ffxx283/VS1053_MP3/VS1053/Code/01_Debug/02_Evl/soundpressure.h

#ifndef SOUNDPRESSURE_H
#define SOUNDPRESSURE_H


u_int16 LinToDB(u_int16 n);
void DrawSoundPressureBars(register s_int16 *samplePair, register u_int16 *levelmem);
void DrawSoundPressureArea();

#endif 
