ffxx283/VS1053_MP3/VS1053/Code/01_Debug/02_Evl/spi.h

#ifndef SPI_H
#define SPI_H

auto u_int16 SpiSend(register __a0 u_int16 dataTopAligned, register __a1 bits);
auto u_int16 SpiTransfer(register __a0 u_int16 dataTopAligned, register __a1 bits);




#endif
