ffxx283/VS1053_MP3/VS1053/Code/01_Debug/02_Evl/vlsilogo.c

#include <vstypes.h>
#include "vlsilogo.h"
const u_int16 vlsilogo[] = {
	0xC618,0xBDF7,0xB5B7,0x6C36,0x3B15,0x3B15,0x7C76,0xBDF7,0xC618,0xC618,0xC618,0xC618,0xC618,0xC618,0xC618,0xC618,0xC618,0xC618,0xC618,0xC618,0xC618,
	0xBDF7,0xA577,0x32F5,0xE75E,0x2AD5,0x9D9A,0xE75E,0x9516,0x9CD3,0x4208,0xC618,0x4208,0x9CD3,0x3186,0xC618,0xC618,0x73AE,0x20E4,0x6B6D,0xC618,0x4A29,
	0xB5D7,0x3B15,0x2AD5,0xE75E,0x9D9A,0x2AD5,0xE75E,0x63D5,0x9CD3,0x20E4,0xC618,0x20E4,0x9CD3,0x20E4,0xC618,0xC618,0x20E4,0xC618,0x7BCF,0xC618,0x20E4,
	0x7C76,0x9D9A,0xE75E,0x2AD5,0x9D9A,0xE75E,0x2AD5,0x63F5,0xC618,0x20E4,0xC618,0x20E4,0xC618,0x20E4,0xC618,0xC618,0x20E4,0xC618,0xC618,0xC618,0x20E4,
	0x4355,0x2AD5,0xE75E,0x9D9A,0x2AD5,0xE75E,0x9D9A,0x94F6,0xC618,0x20E4,0xC618,0x20E4,0xC618,0x20E4,0xC618,0xC618,0x528A,0x20E4,0x6B6D,0xC618,0x20E4,
	0x3B15,0xE75E,0x2AD5,0x9D9A,0xE75E,0x2AD5,0x4335,0xBDD7,0xC618,0x4A29,0x9CD3,0x4A29,0xC618,0x20E4,0xC618,0xC618,0xC618,0xC618,0x20E4,0xC618,0x20E4,
	0x53B5,0xE75E,0x9D9A,0x2AD5,0xE75E,0x32F5,0xA577,0xBDF7,0xC618,0x9CD3,0x3186,0x9CD3,0xC618,0x20E4,0xC618,0xC618,0x7BEF,0xC618,0x20E4,0xC618,0x20E4,
	0xAD97,0x4335,0x2AD5,0x32D5,0x5395,0xAD97,0xBDF7,0xC618,0xC618,0xC618,0x20E4,0xC618,0xC618,0x20E4,0x20E4,0x5ACB,0x73AE,0x20E4,0x6B6D,0xC618,0x4A29,
};
